F4JNT-AF/CM108_Radio_Interface/Images/20250118_133245.jpg

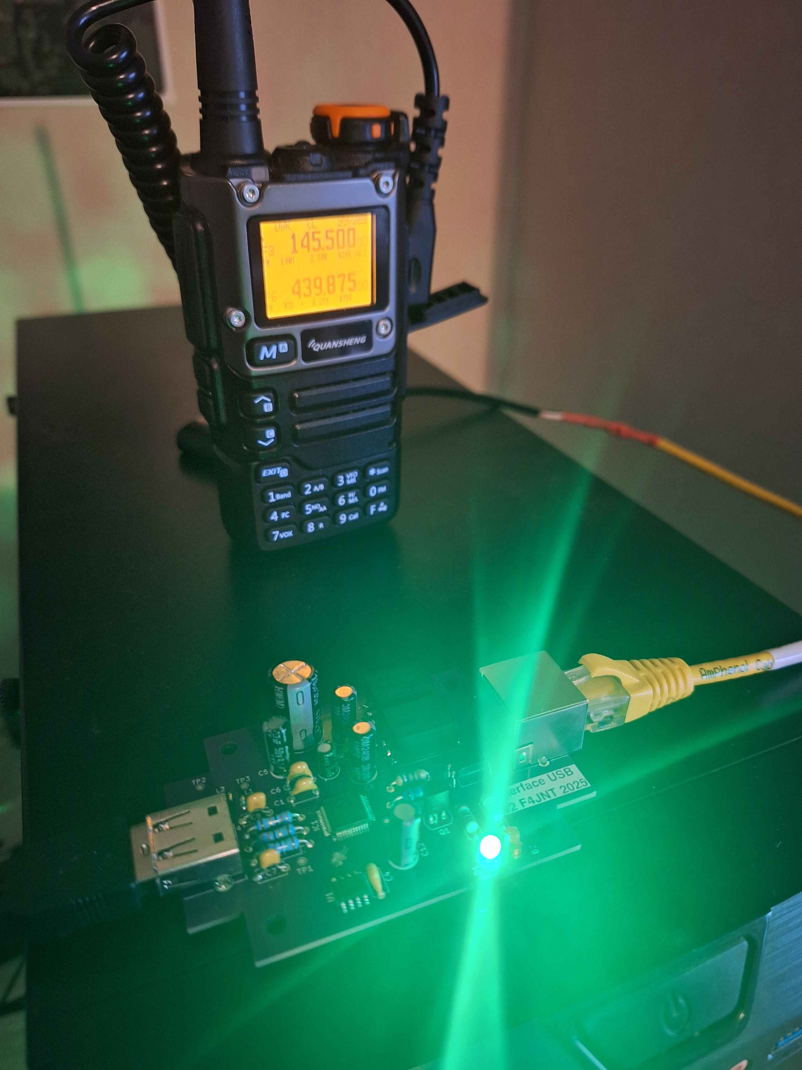
Images/20250118_133245.jpg
